K1P5/240-HEPA-Enclosure/Generic HEPA Filter reference images/Filter Reference Image B.jpg

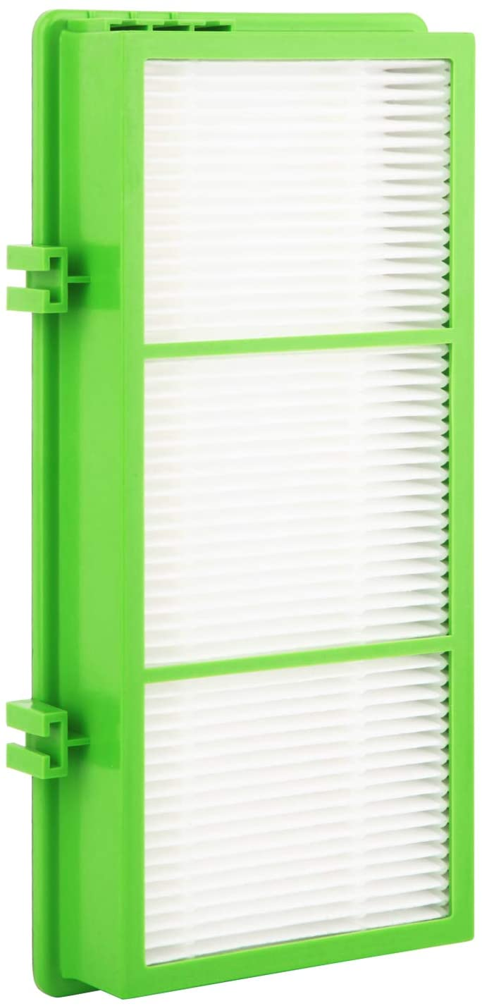
Generic HEPA Filter reference images/Filter Reference Image B.jpg
