K1P5/240-HEPA-Enclosure/Assembly reference images/20200914_174946.jpg

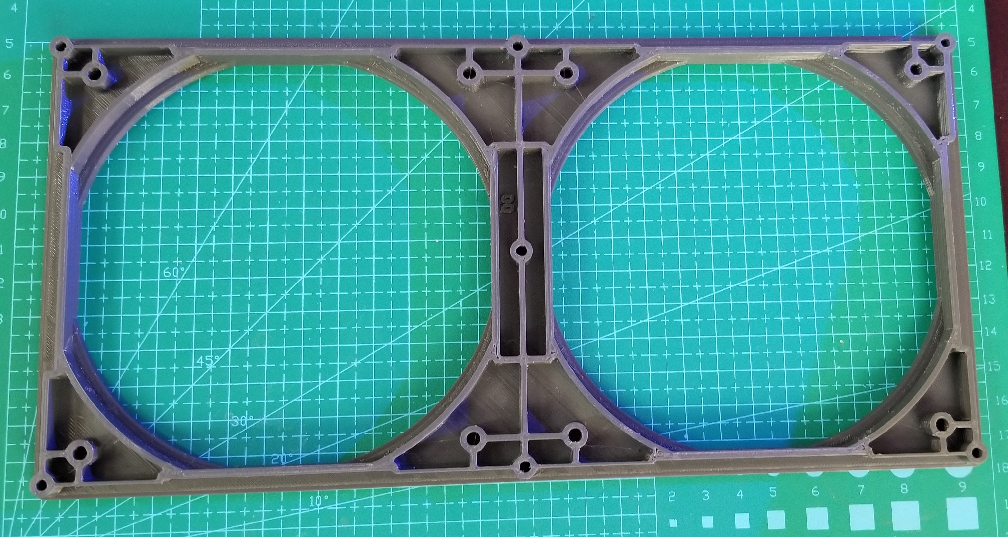
Assembly reference images/20200914_174946.jpg
