K1P5/240-HEPA-Enclosure/Assembly reference images/20200914_181637.jpg

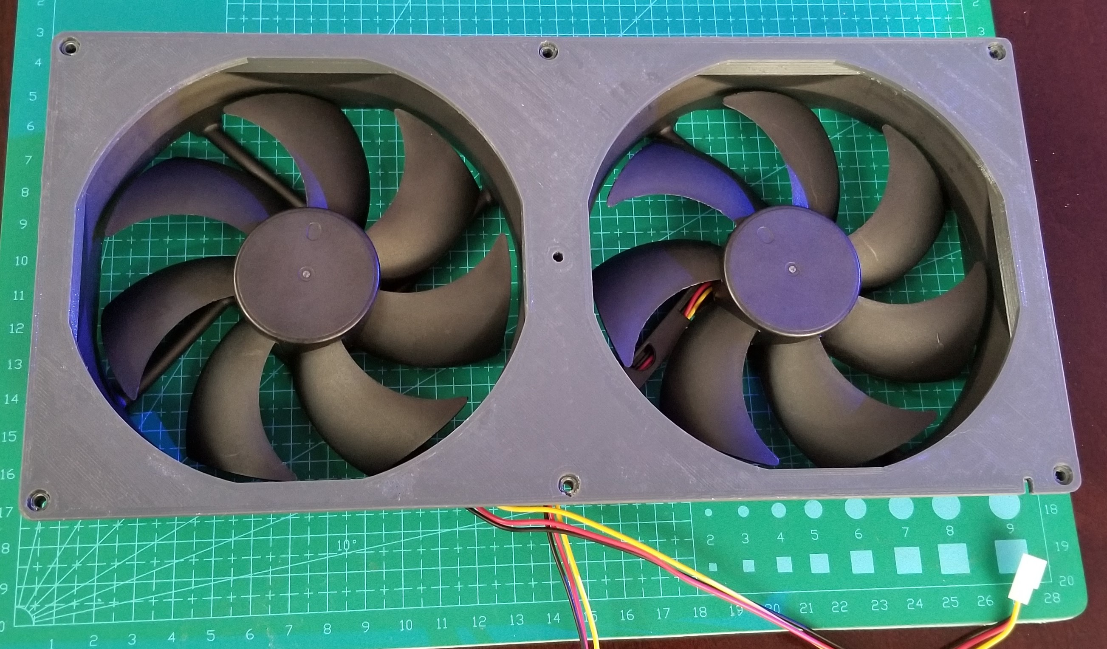
Assembly reference images/20200914_181637.jpg
