K1P5/240-HEPA-Enclosure/Assembly reference images/20200915_175725.jpg

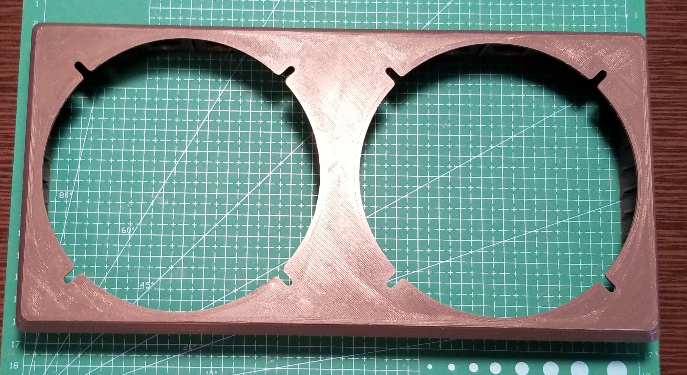
Assembly reference images/20200915_175725.jpg
