K1P5/240-HEPA-Enclosure/Assembly reference images/20200915_191140.jpg

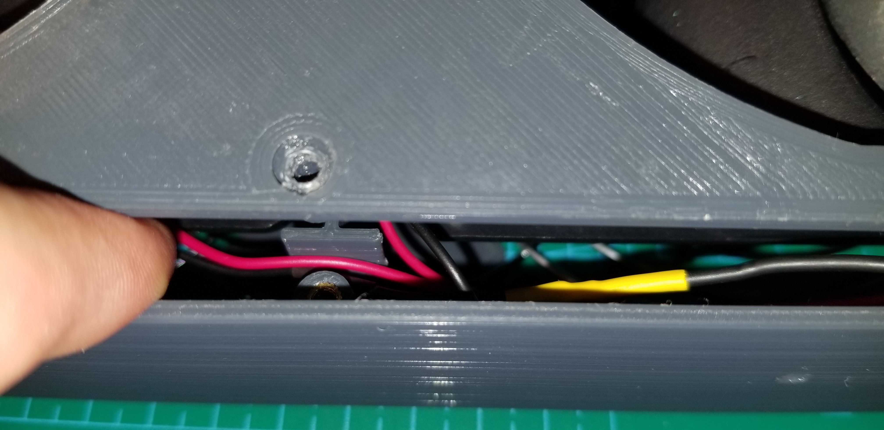
Assembly reference images/20200915_191140.jpg
