K1P5/240-HEPA-Enclosure/Assembly reference images/20200921_171619.jpg

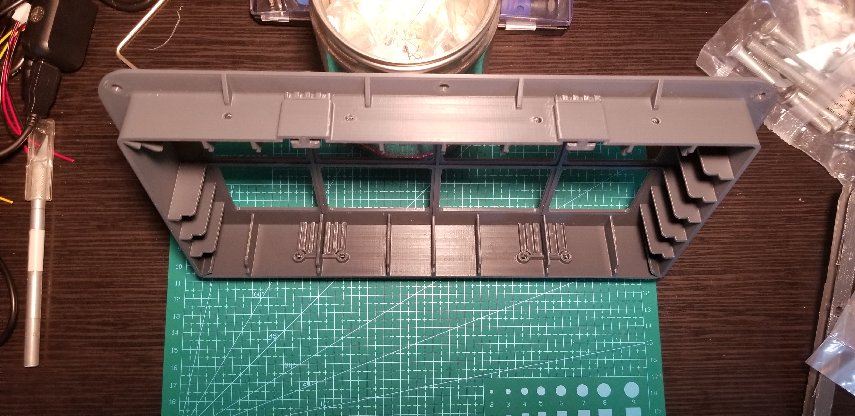
Assembly reference images/20200921_171619.jpg
