K1P5/240-HEPA-Enclosure/Assembly reference images/20200921_180926.jpg

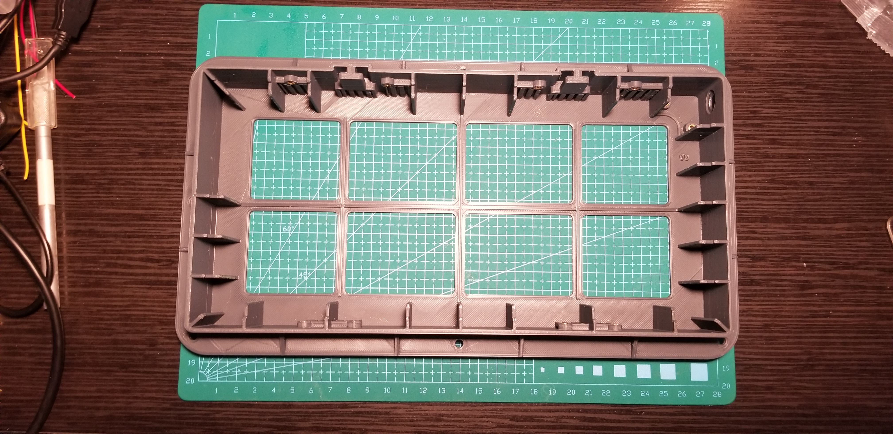
Assembly reference images/20200921_180926.jpg
