K1P5/240-HEPA-Enclosure/Assembly reference images/20200921_181010.jpg

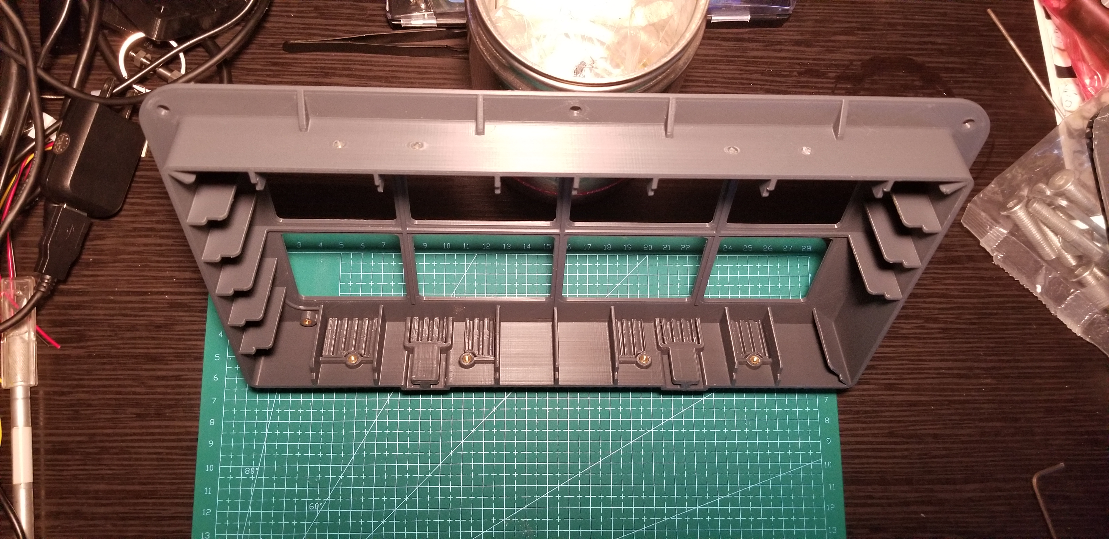
Assembly reference images/20200921_181010.jpg
