K1P5/240-HEPA-Enclosure/Assembly reference images/20200922_171744.jpg

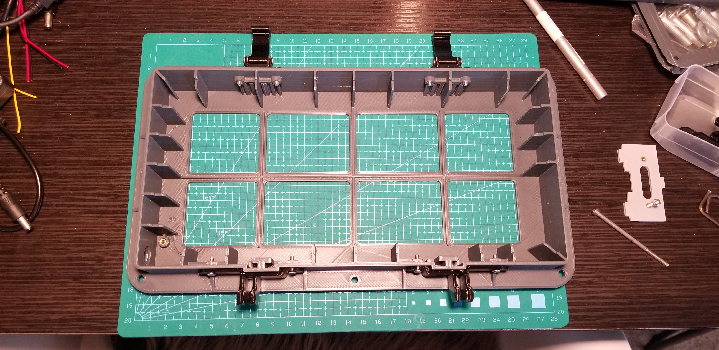
Assembly reference images/20200922_171744.jpg
