K1P5/240-HEPA-Enclosure/Assembly reference images/20200922_201138.jpg

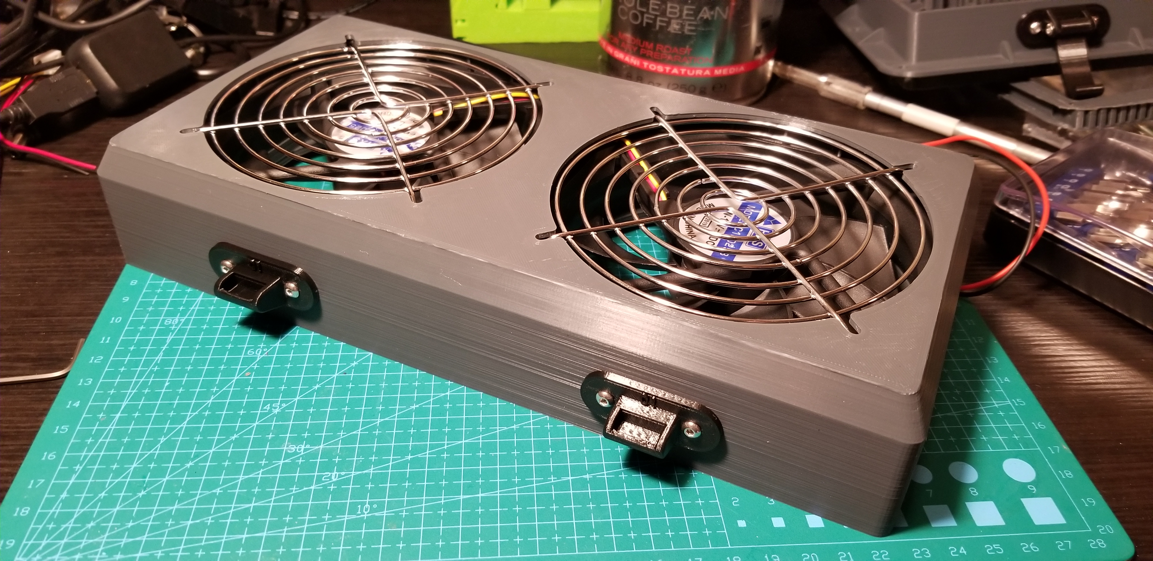
Assembly reference images/20200922_201138.jpg
