K1P5/240-HEPA-Enclosure/Assembly reference images/20200922_203134.jpg

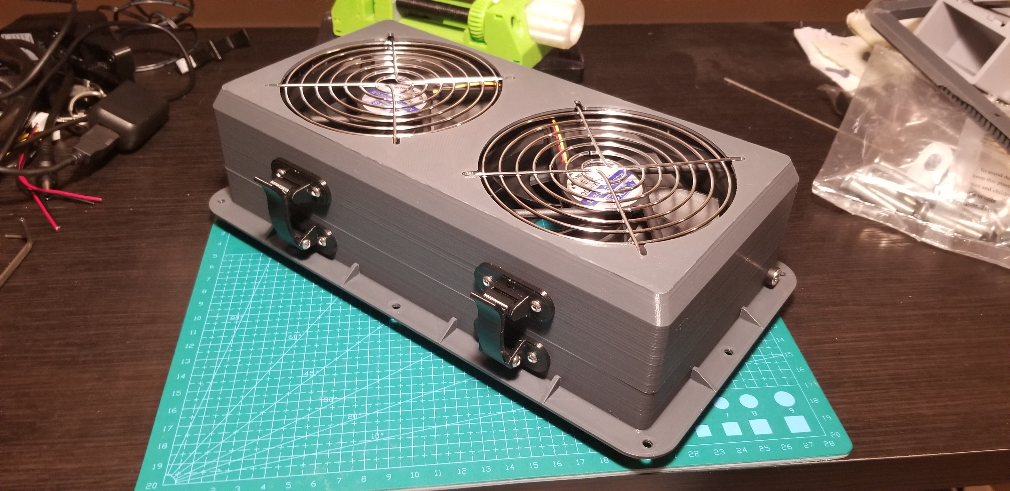
Assembly reference images/20200922_203134.jpg
